max2058/WortUhr_DE_HSB/02_Konstruktion_und_Layouts/25x25cm/Rahmen/Rahmen05.jpg

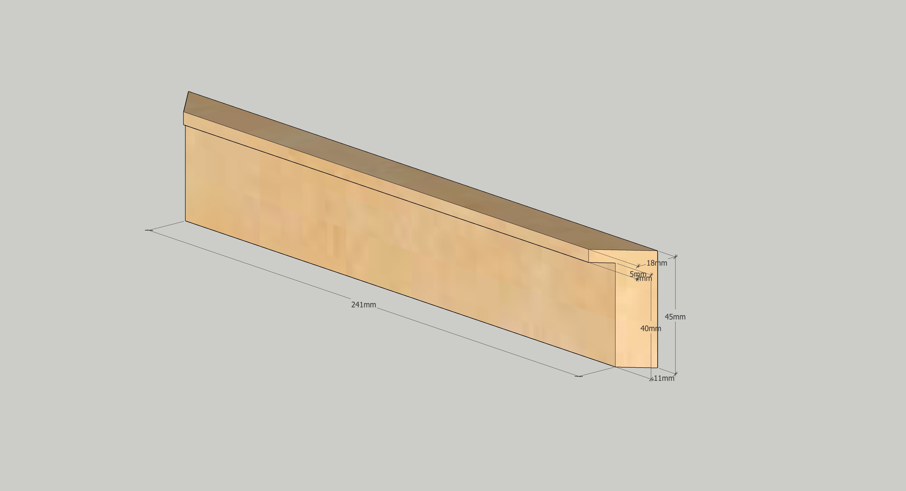
02_Konstruktion_und_Layouts/25x25cm/Rahmen/Rahmen05.jpg
