max2058/WortUhr_DE_HSB/10_Inbetriebnahme/01_Bilder/Bildschirmfoto 2022-04-28 um 17.10.36.png

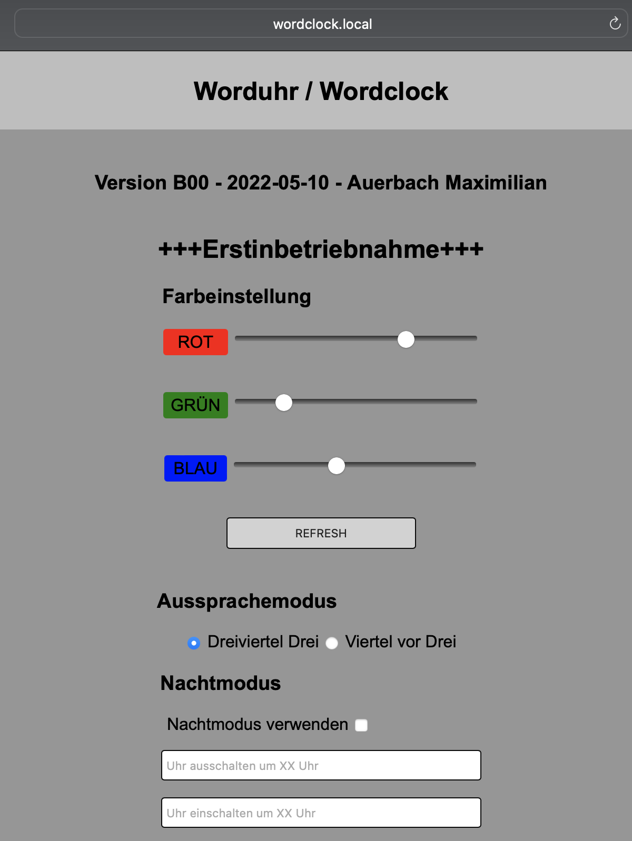
10_Inbetriebnahme/01_Bilder/Bildschirmfoto 2022-04-28 um 17.10.36.png
